atctwo/watch-II/main/states/state_weather.cpp

#include "states.h"

void getLatLong(double &latitude, double &longitude)
{
    EXT_RAM_ATTR latitude = 0;
    EXT_RAM_ATTR longitude = 0;

    if (watch2::wifi_state != 3) // wifi not connected
    {
        ESP_LOGD(WATCH2_TAG, "[weather] not connected to wifi");
    }
    else // wifi is connected
    {
        ESP_LOGD(WATCH2_TAG, "[weather] getting current weather");

        HTTPClient *http = new HTTPClient();
        char server[150];
        std::string api_key = watch2::getApiKey("openweather");
        ESP_LOGD(WATCH2_TAG, "[weather] key: %s", api_key.c_str());
        sprintf(server, "http://api.openweathermap.org/data/2.5/weather?q=%s&appid=%s", watch2::weather_location.c_str(), api_key.c_str());
        ESP_LOGD(WATCH2_TAG, "[weather] server request: %s", server);

        // connect to server
        ESP_LOGD(WATCH2_TAG, "[weather] connecting to server");
        http->begin(watch2::wifi_client, server);
        int http_code = http->GET();
        if (http_code)
        {
            ESP_LOGD(WATCH2_TAG, "[weather] connected to server");
            ESP_LOGD(WATCH2_TAG, "[weather] http code: %d (%s)", http_code, http->errorToString(http_code));

            if (http_code > 0)
            {
                if (http_code == HTTP_CODE_OK)
                {
                    // get server response
                    String res = http->getString();
                    ESP_LOGD(WATCH2_TAG, "[weather] response:");
                    ESP_LOGD(WATCH2_TAG, "%s", res.c_str());

                    // parse returned json
                    cJSON *weather_data = cJSON_Parse(res.c_str());
                    if (weather_data)
                    {
                        // get coord object
                        cJSON *coord_object = cJSON_GetObjectItem(weather_data, "coord");
                        if (coord_object)
                        {
                            // get the latitude and longitude
                            latitude = cJSON_GetObjectItem(coord_object, "lat")->valuedouble;
                            longitude = cJSON_GetObjectItem(coord_object, "lon")->valuedouble;
                        }
                        else
                        {
                            ESP_LOGD(WATCH2_TAG, "[weather] failed to get coord object");
                        }                        
                    }
                    else
                    {
                        ESP_LOGD(WATCH2_TAG, "[weather] failed to parse response");
                    }
                    
                    // free memory used by parsed json
                    cJSON_Delete(weather_data);
                }
            }
            else ESP_LOGD(WATCH2_TAG, "[weather] ???");
            
        }
        else
        {
            ESP_LOGD(WATCH2_TAG, "[weather] failed to connect");
        }

        delete http;
        ESP_LOGD(WATCH2_TAG, "[weather] finished");
    }
    
}

cJSON *getForecast(double latitude, double longitude)
{
    cJSON *forecast = NULL;

    if (watch2::wifi_state != 3) // wifi not connected
    {
        ESP_LOGD(WATCH2_TAG, "[weather] not connected to wifi");
    }
    else // wifi is connected
    {
        ESP_LOGD(WATCH2_TAG, "[weather] getting current weather");

        HTTPClient *http = new HTTPClient();
        char server[175];
        std::string api_key = watch2::getApiKey("openweather");
        ESP_LOGD(WATCH2_TAG, "[weather] key: %s", api_key.c_str());
        sprintf(server, "http://api.openweathermap.org/data/2.5/onecall?lat=%f&lon=%f&exclude=minutely,current,hourly&appid=%s", latitude, longitude, api_key.c_str());
        ESP_LOGD(WATCH2_TAG, "[weather] server request: %s", server);

        // connect to server
        ESP_LOGD(WATCH2_TAG, "[weather] connecting to server");
        http->begin(watch2::wifi_client, server);
        int http_code = http->GET();
        if (http_code)
        {
            ESP_LOGD(WATCH2_TAG, "[weather] connected to server");
            ESP_LOGD(WATCH2_TAG, "[weather] http code: %d (%s)", http_code, http->errorToString(http_code));

            if (http_code > 0)
            {
                if (http_code == HTTP_CODE_OK)
                {
                    // get server response
                    String res = http->getString();
                    ESP_LOGD(WATCH2_TAG, "[weather] response:");
                    ESP_LOGD(WATCH2_TAG, "%s", res.c_str());

                    // parse returned json
                    forecast = cJSON_Parse(res.c_str());
                    if (forecast)
                    {
                        ESP_LOGD(WATCH2_TAG, "[weather] parsed response successfully");                      
                    }
                    else
                    {
                        ESP_LOGD(WATCH2_TAG, "[weather] failed to parse response");
                    }
                }
            }
            else ESP_LOGD(WATCH2_TAG, "[weather] ???");
            
        }
        else
        {
            ESP_LOGD(WATCH2_TAG, "[weather] failed to connect");
        }

        delete http;
        ESP_LOGD(WATCH2_TAG, "hi");
    }

    ESP_LOGD(WATCH2_TAG, "[weather] finished");
    ESP_LOGD(WATCH2_TAG, "aaa");
    return forecast;
    
}

cJSON *getDailyArray(cJSON *forecast)
{
    cJSON *daily_array;

    if (forecast)
    {
        daily_array = cJSON_GetObjectItem(forecast, "daily");
        if (!daily_array) ESP_LOGD(WATCH2_TAG, "[weather] couldn't get daily array");
    }
    else
    {
        ESP_LOGD(WATCH2_TAG, "[weather] forecast is null");
    }

    return daily_array;
}

void state_func_weather()
{

    static cJSON *forecast;
    static cJSON *daily_array;
    static uint8_t selected_day = 0;
    static uint8_t day_page = 0;
    static double latitude = 0;
    static double longitude = 0;
    static uint8_t selected_x = 0;
    static uint8_t selected_y = 0;

    static uint8_t padding = 10;
    static uint8_t button_icon_size = 20;
    static uint16_t day_width = (SCREEN_WIDTH / 2) - (padding * 1.5);
    static uint16_t day_height = (SCREEN_HEIGHT - watch2::top_thing_height - button_icon_size - (padding * 5)) / 4;
    static uint16_t day_radius = 7;
    static TFT_eSprite wind_arrow = TFT_eSprite(&watch2::oled);

    if (watch2::states[watch2::state].variant == 0) // 8 day forecast
    {
        if (!watch2::state_init)
        {
            if (watch2::wifi_state != 3) // not connected to wifi
            {
                watch2::dimScreen(true, 250);
                if (watch2::messageBox("Not connected to\nWifi :(") == 0) 
                {
                    watch2::switchState(-1);
                    return;
                }
            }

            if (watch2::weather_location.isEmpty()) // if no weather location has been set
            {
                ESP_LOGD(WATCH2_TAG, "[weather] location has not been set");

                watch2::dimScreen(true, 250);
                if (watch2::messageBox("Location isn't set.\nDo you want to\nset it?", {"Yes", "No"}) == 0) 
                {
                    std::string location = watch2::textFieldDialogue("Location", watch2::weather_location.c_str());
                    if (location.empty())
                    {
                        // do nothing
                    }
                    else
                    {
                        watch2::weather_location = String(location.c_str());
                        watch2::preferences.begin("watch2");
                        watch2::preferences.putString("weather_city", watch2::weather_location); 
                        watch2::preferences.end();
                    }
                }
            }
            else
            {
                // get latitude and longitude
                getLatLong(latitude, longitude);
                ESP_LOGD(WATCH2_TAG, "[weather] latitude: %f, longitude: %f", latitude, longitude);

                // get forecast
                forecast = getForecast(latitude, longitude);
                daily_array = getDailyArray(forecast);
            }

            // set up wind arrow
            wind_arrow.setColorDepth(16);
            wind_arrow.createSprite(20, 20);
            wind_arrow.setPivot(10, 10);
            wind_arrow.fillSprite(BLACK);
            watch2::drawImage((*watch2::icons)["wind_arrow"], 0, 0, 1.0, 0, wind_arrow);
        }

        if (dpad_left_active())
        {
            if (selected_x == 0) selected_x = 1;
            else selected_x--;
        }
        if (dpad_right_active())
        {
            if (selected_x == 1) selected_x = 0;
            else selected_x++;
        }
        if (dpad_up_active())
        {
            if (selected_y == 0) selected_y = 4;
            else selected_y--;
        }
        if (dpad_down_active())
        {
            if (selected_y == 4) selected_y = 0;
            else selected_y++;
        }

        if (dpad_enter_active())
        {
            if (selected_x == 0 && selected_y == 0) // update location
            {
                std::string location = watch2::textFieldDialogue("Location", watch2::weather_location.c_str());
                if (location.empty())
                {
                    // do nothing
                }
                else
                {
                    watch2::weather_location = String(location.c_str());
                    watch2::preferences.begin("watch2");
                    watch2::preferences.putString("weather_city", watch2::weather_location); 
                    watch2::preferences.end();
                }
            }

            else if (selected_x == 1 && selected_y == 0) // exit app
            {
                if (forecast) cJSON_Delete(forecast);
                watch2::switchState(-1);
            }

            else {

                selected_day = ((selected_y - 1) * 2) + selected_x;
                watch2::switchState(watch2::state, 1);  // switch to details

            }
        }

        draw(dpad_any_active(), {

            // draw location
            watch2::oled.setTextColor(WHITE, BLACK);
            watch2::oled.setCursor(0, watch2::top_thing_height);
            watch2::oled.print(watch2::weather_location);

            // draw icons
            watch2::oled.drawBitmap(
                SCREEN_WIDTH - button_icon_size, watch2::top_thing_height, 
                (*watch2::small_icons)["key_cancel"].data(), button_icon_size, button_icon_size, (selected_y == 0 && selected_x == 1)?watch2::themecolour:WHITE
            );
            watch2::oled.drawBitmap(
                SCREEN_WIDTH - (button_icon_size * 2) - padding, watch2::top_thing_height, 
                (*watch2::small_icons)["key_symbols"].data(), button_icon_size, button_icon_size, (selected_y == 0 && selected_x == 0)?watch2::themecolour:WHITE
            );

            // draw days
            uint16_t x = padding, y = watch2::top_thing_height + button_icon_size + padding;
            for (uint8_t i = 0; i < 8; i++)
            {
                // numbers
                uint8_t current_x = i % 2;
                uint8_t current_y = i / 2;
                uint16_t colour = ( ( current_x == selected_x && current_y == (selected_y - 1)) ? watch2::themecolour : WHITE );

                uint16_t x_position = x + ( (day_width + padding)  * current_x);
                uint16_t y_position = y + ( (day_height + padding) * current_y);

                // draw outline
                watch2::oled.drawRoundRect(x_position, y_position, day_width, day_height, day_radius, colour);

                // draw name and weather
                if (daily_array)
                {
                    cJSON *day_object = cJSON_GetArrayItem(daily_array, i);
                    if (day_object)
                    {
                        // draw day
                        time_t dt = cJSON_GetObjectItem(day_object, "dt")->valueint;
                        watch2::oled.setTextDatum(CL_DATUM);
                        watch2::oled.setTextColor(WHITE, BLACK);
                        watch2::oled.drawString(dayShortStr(weekday(dt)), x_position + padding, y_position + (day_height / 2));
                        watch2::oled.setTextDatum(TL_DATUM);

                        // draw weather icon
                        cJSON *weather_array = cJSON_GetObjectItem(day_object, "weather");
                        if (weather_array)
                        {
                            cJSON *primary_weather = cJSON_GetArrayItem(weather_array, 0);
                            int weather_id = cJSON_GetObjectItem(primary_weather, "id")->valueint;

                            // this assumes all the weather icons are the same dimensions
                            // if the icons were to be different sizes, the next two lines would have to be called
                            // in each switch statement case
                            uint16_t weather_icon_x = (x_position + day_width) - padding - (*watch2::icons)["rain"].width;
                            uint16_t weather_icon_y = (y_position + (day_height / 2)) - ((*watch2::icons)["rain"].height / 2);

                            switch(weather_id / 100)
                            {
                                case 2: // thunder
                                    drawImage((*watch2::icons)["thunder"], weather_icon_x, weather_icon_y);
                                    break;
                                    
                                case 3: // drizzle
                                    drawImage((*watch2::icons)["sun_rain"], weather_icon_x, weather_icon_y);
                                    break;

                                case 5: // rain
                                    drawImage((*watch2::icons)["rain"], weather_icon_x, weather_icon_y);
                                    break;

                                case 6: // snow
                                    drawImage((*watch2::icons)["snow"], weather_icon_x, weather_icon_y);
                                    break;

                                case 7: // atmosphere
                                    drawImage((*watch2::icons)["wind"], weather_icon_x, weather_icon_y);
                                    break;

                                case 8: // clear / clouds
                                    if (weather_id == 800) // clear
                                    {
                                        drawImage((*watch2::icons)["sun"], weather_icon_x, weather_icon_y);
                                    }
                                    else
                                    {
                                        drawImage((*watch2::icons)["sun_cloud"], weather_icon_x, weather_icon_y);
                                    }
                                    break;

                                default:
                                    drawImage((*watch2::icons)["weather_unknown"], weather_icon_x, weather_icon_y);
                                    break;
                            }
                        }
                        else ESP_LOGD(WATCH2_TAG, "[weather] failed to get weather array");
                    }
                    else ESP_LOGD(WATCH2_TAG, "[weather] couldn't get information for day %d", i);

                    
                }
            }

        });
    }
    else if (watch2::states[watch2::state].variant == 1) // daily forecast
    {
        if (!watch2::state_init)
        {
            watch2::oled.setCursor(0, watch2::top_thing_height);
            if (daily_array)
            {
                cJSON *day_object = cJSON_GetArrayItem(daily_array, selected_day);
                if (day_object)
                {
                    // draw date
                    uint32_t dt = cJSON_GetObjectItem(day_object, "dt")->valueint;
                    watch2::oled.setTextColor(watch2::themecolour, BLACK);
                    watch2::oled.printf("%s %d ", dayStr(weekday(dt)), day(dt));
                    watch2::oled.printf("%s\n", monthStr(month(dt)));

                    // draw weather icon
                    cJSON *weather_array = cJSON_GetObjectItem(day_object, "weather");
                    if (weather_array)
                    {
                        cJSON *primary_weather = cJSON_GetArrayItem(weather_array, 0);
                        int weather_id = cJSON_GetObjectItem(primary_weather, "id")->valueint;

                        // this assumes all the weather icons are the same dimensions
                        // if the icons were to be different sizes, the next two lines would have to be called
                        // in each switch statement case
                        uint16_t weather_icon_x = SCREEN_WIDTH - (*watch2::icons)["rain"].width;
                        uint16_t weather_icon_y = watch2::top_thing_height;

                        switch(weather_id / 100)
                        {
                            case 2: // thunder
                                drawImage((*watch2::icons)["thunder"], weather_icon_x, weather_icon_y);
                                break;
                                
                            case 3: // drizzle
                                drawImage((*watch2::icons)["sun_rain"], weather_icon_x, weather_icon_y);
                                break;

                            case 5: // rain
                                drawImage((*watch2::icons)["rain"], weather_icon_x, weather_icon_y);
                                break;

                            case 6: // snow
                                drawImage((*watch2::icons)["snow"], weather_icon_x, weather_icon_y);
                                break;

                            case 7: // atmosphere
                                drawImage((*watch2::icons)["wind"], weather_icon_x, weather_icon_y);
                                break;

                            case 8: // clear / clouds
                                if (weather_id == 800) // clear
                                {
                                    drawImage((*watch2::icons)["sun"], weather_icon_x, weather_icon_y);
                                }
                                else
                                {
                                    drawImage((*watch2::icons)["sun_cloud"], weather_icon_x, weather_icon_y);
                                }
                                break;

                            default:
                                drawImage((*watch2::icons)["weather_unknown"], weather_icon_x, weather_icon_y);
                                break;
                        }
                    }
                    else ESP_LOGD(WATCH2_TAG, "[weather] failed to get weather array");

                    if (day_page == 0)
                    {
                        // draw temperature
                        cJSON *temp = cJSON_GetObjectItem(day_object, "temp");
                        double temp_min = cJSON_GetObjectItem(temp, "min")->valuedouble - 273.5;
                        double temp_max = cJSON_GetObjectItem(temp, "max")->valuedouble - 273.5;
                        double temp_day = cJSON_GetObjectItem(temp, "day")->valuedouble - 273.5;

                        watch2::oled.setTextColor(WHITE, BLACK);
                        watch2::oled.print("High Temp: ");
                        watch2::oled.setTextColor(watch2::themecolour, BLACK);
                        watch2::oled.printf("%0.2f °C\n", temp_max);

                        watch2::oled.setTextColor(WHITE, BLACK);
                        watch2::oled.print("Low Temp: ");
                        watch2::oled.setTextColor(watch2::themecolour, BLACK);
                        watch2::oled.printf("%0.2f °C\n", temp_min);

                        watch2::oled.setTextColor(WHITE, BLACK);
                        watch2::oled.print("Day Temp: ");
                        watch2::oled.setTextColor(watch2::themecolour, BLACK);
                        watch2::oled.printf("%0.2f °C\n", temp_day);

                        // draw pressure
                        uint32_t pressure = cJSON_GetObjectItem(day_object, "pressure")->valueint;
                        watch2::oled.setTextColor(WHITE, BLACK);
                        watch2::oled.print("Pressure: ");
                        watch2::oled.setTextColor(watch2::themecolour, BLACK);
                        watch2::oled.printf("%d hPa\n", pressure);

                        // draw humidity
                        uint32_t humidity = cJSON_GetObjectItem(day_object, "humidity")->valueint;
                        watch2::oled.setTextColor(WHITE, BLACK);
                        watch2::oled.print("Humidity: ");
                        watch2::oled.setTextColor(watch2::themecolour, BLACK);
                        watch2::oled.printf("%d%%\n", humidity);

                        // draw rain
                        cJSON *rain = cJSON_GetObjectItem(day_object, "rain");
                        if (rain)
                        {
                            watch2::oled.setTextColor(WHITE, BLACK);
                            watch2::oled.print("Rain: ");
                            watch2::oled.setTextColor(watch2::themecolour, BLACK);
                            watch2::oled.printf("%0.3f mm\n", rain->valuedouble);
                        }

                        // draw snow
                        cJSON *snow = cJSON_GetObjectItem(day_object, "snow");
                        if (snow)
                        {
                            watch2::oled.setTextColor(WHITE, BLACK);
                            watch2::oled.print("Snow: ");
                            watch2::oled.setTextColor(watch2::themecolour, BLACK);
                            watch2::oled.printf("%0.3f mm\n", snow->valuedouble);
                        }
                    }
                    else if (day_page == 1)
                    {
                        // draw sunrise and sunset
                        uint32_t sunrise = cJSON_GetObjectItem(day_object, "sunrise")->valueint;
                        watch2::oled.setTextColor(WHITE, BLACK);
                        watch2::oled.print("Sunrise: ");
                        watch2::oled.setTextColor(watch2::themecolour, BLACK);
                        watch2::oled.printf("%2d:%2d\n", hour(sunrise), minute(sunrise));

                        uint32_t sunset = cJSON_GetObjectItem(day_object, "sunset")->valueint;
                        watch2::oled.setTextColor(WHITE, BLACK);
                        watch2::oled.print("Sunset:  ");
                        watch2::oled.setTextColor(watch2::themecolour, BLACK);
                        watch2::oled.printf("%2d:%2d\n", hour(sunset), minute(sunset));

                        // draw clouds
                        uint32_t clouds = cJSON_GetObjectItem(day_object, "clouds")->valueint;
                        watch2::oled.setTextColor(WHITE, BLACK);
                        watch2::oled.print("Clouds: ");
                        watch2::oled.setTextColor(watch2::themecolour, BLACK);
                        watch2::oled.printf("%d%%\n", clouds);

                        // draw dew point
                        double dew_point = cJSON_GetObjectItem(day_object, "dew_point")->valuedouble - 273.5;
                        watch2::oled.setTextColor(WHITE, BLACK);
                        watch2::oled.print("Dew Point: ");
                        watch2::oled.setTextColor(watch2::themecolour, BLACK);
                        watch2::oled.printf("%0.2f °C\n", dew_point);

                        // draw wind speed
                        double wind_speed = cJSON_GetObjectItem(day_object, "wind_speed")->valuedouble * MPS_TO_MPH;
                        watch2::oled.setTextColor(WHITE, BLACK);
                        watch2::oled.print("Wind Speed: ");
                        watch2::oled.setTextColor(watch2::themecolour, BLACK);
                        watch2::oled.printf("%0.2f mph\n", wind_speed);

                        // draw wind direction
                        uint32_t wind_deg = cJSON_GetObjectItem(day_object, "wind_deg")->valueint;
                        watch2::oled.setTextColor(WHITE, BLACK);
                        watch2::oled.print("Wind Direction: ");
                        watch2::oled.setTextColor(watch2::themecolour, BLACK);
                        watch2::oled.printf("%d °\n", wind_deg);

                        watch2::oled.setPivot(
                            watch2::oled.textWidth("Wind Direction: 999°") + 20, 
                            watch2::top_thing_height + (watch2::oled.fontHeight() * 6) + 10
                        );
                        wind_arrow.pushRotated(wind_deg, BLACK);
                        //wind_arrow.pushSprite(100, 100);

                        // draw uv index
                        double uvi = cJSON_GetObjectItem(day_object, "uvi")->valuedouble;
                        watch2::oled.setTextColor(WHITE, BLACK);
                        watch2::oled.print("UV Index: ");
                        watch2::oled.setTextColor(watch2::themecolour, BLACK);
                        watch2::oled.printf("%0.2f\n", uvi);
                    }
                }
                else 
                {
                    ESP_LOGD(WATCH2_TAG, "[weather] couldn't get day from array (selected_day: %d)", selected_day);
                    watch2::oled.printf("error: couldn't get \nday from array \n(selected_day: %d)\n", selected_day);
                }
            }
            else 
            {
                ESP_LOGD(WATCH2_TAG, "[weather] invalid daily array");
                watch2::oled.println("error: invalid daily \narray");
            }

            
        }

        if (dpad_left_active() || dpad_right_active())
        {
            if (day_page == 0) day_page = 1;
            else day_page = 0;
            watch2::switchState(watch2::state, 1);
        }

        if (dpad_any_active())
        {
            watch2::switchState(watch2::state, 0);
        }
    }

    watch2::drawTopThing();

}
