atctwo/watch-II/main/states/state_timer.cpp

#include "states.h"

void state_func_timer()
{
    static int selected_timer = -1;
    static int selected_button = 3;
    static int last_selected_timer = -2;
    //0 - hours
    //1 - minutes
    //2 - seconds
    //3 - play / pause (or back if on timer -1)
    //4 - delete (or add if on timer -1)
    EXT_RAM_ATTR static char text_aaaa[150];
    EXT_RAM_ATTR static int16_t x1, y1;
    EXT_RAM_ATTR static uint16_t w=0, h=0;
    EXT_RAM_ATTR static uint16_t width_two_digits = 0, width_two_digits_colon = 0, width_three_digits_colon = 0;

    if (!watch2::state_init)
    {
        //watch2::oled.setFreeFont(&SourceSansPro_Regular6pt7b);

        //calculate sizes of digit things
        watch2::getTextBounds("99", 0, 0, &x1, &y1, &width_two_digits, &h);
        watch2::getTextBounds(": 99", 0, 0, &x1, &y1, &width_two_digits_colon, &h);
        watch2::getTextBounds(": 999", 0, 0, &x1, &y1, &width_three_digits_colon, &h);

    }

    if (dpad_left_active())
    {
        selected_button--;
        if (selected_button < 0) selected_button = 4;
        if (selected_timer == -1 && selected_button < 2) selected_button = 4;
    }

    if (dpad_right_active())
    {
        selected_button++;
        if (selected_button > 4) selected_button = 0;
        if (selected_timer == -1 && selected_button < 2) selected_button = 2;
    }

    if (dpad_down_active())
    {
        if (selected_timer == -1 || selected_button == 3 || selected_button == 4)
        {
            selected_timer++;
            if (selected_timer >= watch2::timers.size()) selected_timer = -1;
        }
        else //decrease time
        {
            if (floor(watch2::timers[selected_timer].duration / 3600) > 0)
            if (selected_button == 0) watch2::timers[selected_timer].duration -= 3600;      //hours
            if (floor(watch2::timers[selected_timer].duration % 3600 / 60) > 0)
            if (selected_button == 1) watch2::timers[selected_timer].duration -= 60;        //minutes
            if (floor(watch2::timers[selected_timer].duration % 3600 % 60) > 0)
            if (selected_button == 2) watch2::timers[selected_timer].duration -= 1;         //seconds
            if (watch2::timers[selected_timer].alarm_id != 255) Alarm.write(watch2::timers[selected_timer].alarm_id, watch2::timers[selected_timer].duration); //reset timer with new duration
            else watch2::timers[selected_timer].initial_duration = watch2::timers[selected_timer].duration;
        }
    }

    if (dpad_up_active())
    {
        if (selected_timer == -1 || selected_button == 3 || selected_button == 4)
        {
            selected_timer--;
            if (selected_timer < -1) selected_timer = watch2::timers.size() - 1;
        }
        else //increase time
        {
            if (selected_button == 0) watch2::timers[selected_timer].duration += 3600;      //hours
            if (selected_button == 1) watch2::timers[selected_timer].duration += 60;        //minutes
            if (selected_button == 2) watch2::timers[selected_timer].duration += 1;         //seconds
            if (watch2::timers[selected_timer].alarm_id != 255) Alarm.write(watch2::timers[selected_timer].alarm_id, watch2::timers[selected_timer].duration); //reset timer with new duration
            else watch2::timers[selected_timer].initial_duration = watch2::timers[selected_timer].duration;
        }
    }

    if (dpad_enter_active())
    {
        if (selected_timer == -1)
        {
            //add new timer
            if (selected_button == 4)
            {
                watch2::timers.push_back({
                    30,     //duration in seconds
                    30,     //initial duration (used when a timer ends)
                    255,    //alarm id (255 means that no TimeAlarms timer has been created)
                    -1,     //time started
                    [](){   //function to execute once timer has ended
                        AlarmID_t id = Alarm.getTriggeredAlarmId();
                        int timer_id = -1;
                        for (int i = 0; i < watch2::timers.size(); i++)
                        {
                            if (watch2::timers[i].alarm_id == id)
                            {
                                timer_id = i;
                            }
                        }
                        watch2::timers[timer_id].alarm_id = 255;
                        watch2::timers[timer_id].time_started = -1;
                        watch2::timers[timer_id].duration = watch2::timers[timer_id].initial_duration;
                        watch2::timer_trigger_status = 1;
                        watch2::timer_trigger_id = timer_id;
                    },
                    -1      //last value (used for redrawing remaining time)
                });
            }
            else if (selected_button == 2)
            {
                // change timer music
                ESP_LOGD(WATCH2_TAG, "[timers] changing music");
                std::string new_music = watch2::beginFileSelect();
                ESP_LOGD(WATCH2_TAG, "[timers] new music to %s", new_music.c_str());
                watch2::timer_music = String(new_music.c_str());
                ESP_LOGD(WATCH2_TAG, "[timers] changed music to %s", watch2::timer_music.c_str());

                watch2::preferences.begin("watch2");
                watch2::preferences.putString("timer_music", watch2::timer_music);
                watch2::preferences.end();
                ESP_LOGD(WATCH2_TAG, "[timers] updated preferences store");
            }
        }
        else
        {
            if (selected_button == 3) // play / pause timer
            {
                if (watch2::timers[selected_timer].alarm_id == 255) //start timer
                {
                    //create a TimeAlarms timer
                    AlarmID_t id = Alarm.timerOnce(
                        watch2::timers[selected_timer].duration,             //duration in seconds
                        watch2::timers[selected_timer].on_tick_handler       //function to call after time has elapsed
                    );

                    //store timer metadata
                    watch2::timers[selected_timer].alarm_id = id;
                    watch2::timers[selected_timer].time_started = now();
                }
                else                                      //pause timer
                {
                    //store time remaining
                    time_t time_remaining = ( watch2::timers[selected_timer].time_started + Alarm.read(watch2::timers[selected_timer].alarm_id ) ) - now();
                    watch2::timers[selected_timer].duration = time_remaining;

                    //free alarm id (essentially destroying the TimeAlarm timer) and reset stored alarm id and time started
                    Alarm.free(watch2::timers[selected_timer].alarm_id);
                    watch2::timers[selected_timer].alarm_id = 255;
                    watch2::timers[selected_timer].time_started = -1;
                }
            }
            if (selected_button == 4) // remove timer
            {
                //store selected timer
                AlarmID_t whee = selected_timer;

                //change selecte timer to previous timer
                selected_timer--;

                //free alarm id
                Alarm.free(watch2::timers[whee].alarm_id);

                //remove timer from timers
                watch2::timers.erase(watch2::timers.begin() + whee);

                //clear screen
                watch2::oled.fillScreen(BLACK);
            }
        }
    }

    //draw timers
    if (1)
    {
        int timer_x = 2;
        int timer_y = watch2::top_thing_height;
        int timer_w = SCREEN_WIDTH - (timer_x * 2);
        int timer_h = SCREEN_HEIGHT - timer_y;
        int icon_radius = 8;
        int radius = 4;
        int icon_spacing = 3;
        int icon_size = 20;
        int timer_edge = timer_x + timer_w;
        uint16_t working_button_colour = WHITE;
        uint16_t working_timer_colour = WHITE;

        draw(dpad_any_active(), {

            //set colour of row
            working_timer_colour = (selected_timer == -1) ? watch2::themecolour : WHITE;

            //draw header
            watch2::oled.setTextColor(working_timer_colour, BLACK);
            watch2::oled.setCursor(timer_x, timer_y);
            watch2::oled.print("Timers");

            //set colour of music button
            working_button_colour = (selected_button <= 2 && selected_timer == -1) ? watch2::themecolour : WHITE;

            //draw music button
            watch2::oled.drawBitmap(
                timer_edge - (icon_size * 3) - (icon_spacing * 8),
                timer_y,
                (*watch2::small_icons)["small_audio"].data(),
                icon_size,
                icon_size,
                working_button_colour
            );

            //set colour of back button
            working_button_colour = (selected_button == 3 && selected_timer == -1) ? watch2::themecolour : WHITE;

            //draw back button
            watch2::oled.drawBitmap(
                timer_edge - (icon_size * 2) - (icon_spacing * 5),
                timer_y,
                (*watch2::small_icons)["back"].data(),
                icon_size,
                icon_size,
                working_button_colour
            );

            //set colour of add button
            working_button_colour = (selected_button == 4 && selected_timer == -1) ? watch2::themecolour : WHITE;

            //draw add button
            watch2::oled.drawBitmap(
                timer_edge - icon_size - (icon_spacing * 2),
                timer_y,
                (*watch2::small_icons)["add"].data(),
                icon_size,
                icon_size,
                working_button_colour
            );
        });

        //draw timers
        for (int i = 0; i < watch2::timers.size(); i++)
        {
            timer_y += watch2::oled.fontHeight() + (icon_spacing * 2);

            time_t current_time = (watch2::timers[i].alarm_id == 255) ? watch2::timers[i].duration : ( watch2::timers[i].time_started + Alarm.read(watch2::timers[i].alarm_id ) ) - now();
            //if this is the state's first frame, or the time of the timer has changed,
            //or this is the selected timer and any button has been pressed
            draw(dpad_any_active() || current_time != watch2::timers[i].last_value, {
                //clear previous text
                watch2::oled.fillRect(timer_x, timer_y, timer_w - (icon_spacing * 6) - (icon_size * 2), watch2::oled.fontHeight(), BLACK);

                //set colour of row
                working_timer_colour = (selected_timer == i) ? watch2::themecolour : WHITE;

                //get time to display
                time_t time_left = (watch2::timers[i].alarm_id == 255) ? watch2::timers[i].duration : ( watch2::timers[i].time_started + Alarm.read(watch2::timers[i].alarm_id ) ) - now();
                time_t time_left_hrs = floor(time_left / 3600);
                time_t time_left_min = floor(time_left % 3600 / 60);
                time_t time_left_sec = floor(time_left % 3600 % 60);

                /*
                watch2::getTextBounds("99", 0, 0, &x1, &y1, &width_two_digits, &h);
                watch2::getTextBounds(":99", 0, 0, &x1, &y1, &width_two_digits_colon, &h);
                watch2::getTextBounds(":999", 0, 0, &x1, &y1, &width_three_digits_colon, &h);
                */

                //print hours
                watch2::oled.setCursor(timer_x, timer_y);
                watch2::oled.setTextColor(working_timer_colour, BLACK);
                watch2::oled.printf("%02d", time_left_hrs);
                working_button_colour = (selected_button == 0 && selected_timer == i) ? watch2::themecolour : BLACK;
                watch2::oled.drawRoundRect(timer_x - 1, timer_y - 1, width_two_digits + 4, watch2::oled.fontHeight(), icon_radius, working_button_colour);

                //print minutes
                watch2::oled.setCursor(timer_x + (width_two_digits) + 4, timer_y);
                watch2::oled.printf(": %02d", time_left_min);
                working_button_colour = (selected_button == 1 && selected_timer == i) ? watch2::themecolour : BLACK;
                watch2::oled.drawRoundRect(timer_x + (width_two_digits) + 4 - 1, timer_y - 1, width_two_digits_colon + 5, watch2::oled.fontHeight(), icon_radius, working_button_colour);

                //print seconds
                watch2::oled.setCursor(timer_x + width_two_digits + width_two_digits_colon + 2 + 7, timer_y);
                watch2::oled.printf(": %02d", time_left_sec);
                working_button_colour = (selected_button == 2 && selected_timer == i) ? watch2::themecolour : BLACK;
                watch2::oled.drawRoundRect(timer_x + width_two_digits + width_two_digits_colon + 2 + 7 - 1, timer_y - 1, width_two_digits_colon + 5, watch2::oled.fontHeight(), icon_radius, working_button_colour);

                //set colour of play / pause button
                working_button_colour = (selected_button == 3 && selected_timer == i) ? watch2::themecolour : WHITE;

                //draw play / pause button
                watch2::oled.drawBitmap(
                    timer_edge - (icon_size * 2) - (icon_spacing * 5),
                    timer_y,
                    (watch2::timers[i].alarm_id == 255) ? (*watch2::small_icons)["play"].data() : (*watch2::small_icons)["pause"].data(),
                    icon_size,
                    icon_size,
                    working_button_colour
                );

                //set colour of delete button
                working_button_colour = (selected_button == 4 && selected_timer == i) ? watch2::themecolour : WHITE;

                //draw delete button
                watch2::oled.drawBitmap(
                    timer_edge - icon_size - (icon_spacing * 2),
                    timer_y,
                    (*watch2::small_icons)["key_cancel"].data(),
                    icon_size,
                    icon_size,
                    working_button_colour
                );

                watch2::timers[i].last_value = (watch2::timers[i].alarm_id == 255) ? watch2::timers[i].duration : ( watch2::timers[i].time_started + Alarm.read(watch2::timers[i].alarm_id ) ) - now();

            });

        }

    }

    watch2::drawTopThing();

    if (dpad_enter_active())
    {
        if (selected_timer == -1)
        {
            //go back to state menu
            if (selected_button < 4) watch2::switchState(-1);
        }
    }

    last_selected_timer = selected_timer;
}
