atctwo/watch-II/main/states/states.cpp

#include "../watch2.h"
#include "states.h"

namespace watch2
{

    std::vector<stateMeta> states = {

        stateMeta("Initial State", state_func_init, "init.bmp", 0, false, true),
        stateMeta("Watch Face", state_func_watch_face, "watch"),
        stateMeta("State Menu", state_func_state_menu, "menu", 0, false, true),
        stateMeta("Settings", state_func_settings, "settings"),

        stateMeta("Calculator", state_func_calc, "calculator"),
        stateMeta("Stopwatch", state_func_stopwatch, "stopwatch"),
        stateMeta("Timer", state_func_timer, "timer"),
        stateMeta("Alarms", state_func_alarms, "alarms"),
        stateMeta("File Browser", state_func_SDtest, "file_browser"),
        stateMeta("Notepad", state_func_notepad, "notepad"),
        stateMeta("IR remote", state_func_ir_remote, "ir_remote"),
        stateMeta("Image Viewer", state_func_image_viewer, "image_viewer"),
        stateMeta("Weather", state_func_weather, "weather"),
        stateMeta("Wikipedia", state_func_wiki, "wikipedia"),
        stateMeta("Quiz Thingy", state_func_quiz, "quiz"),
        stateMeta("Reddit", state_func_reddit),
        stateMeta("Music Player", state_func_music_player, "music_player"),
        stateMeta("Radio", state_func_radio, "radio"),
        //stateMeta("Recorder", state_func_recorder),
        stateMeta("Bluetooth Remote", state_func_bt_remote, "ble_remote"),
        stateMeta("Sensor Thing", state_func_sensor, "sensors"),
        stateMeta("Tetris", state_func_tetris, "ltris"),
        stateMeta("Snek 2", state_func_snek, "snake"),
        stateMeta("Blackjack", state_func_blackjack, "cards")
        // //stateMeta("NES", state_func_nes, "nes")

    };

}
