atctwo/watch-II/main/watch2_files.cpp

/**
 * @file watch2_files.cpp
 * @author atctwo
 * @brief functions for file system access
 * @version 0.1
 * @date 2020-11-21
 * 
 * @copyright Copyright (c) 2020 atctwo
 * 
 */

#include "watch2.h"

namespace watch2 {

    // files
    EXT_RAM_ATTR int sd_state = 0;
    EXT_RAM_ATTR bool spiffs_state = 0;
    EXT_RAM_ATTR int file_select_status = 0;
    EXT_RAM_ATTR std::string file_path = "/";
    EXT_RAM_ATTR bool file_select_dir_list_init = false;
    
    //SdFat sdcard(&*vspi);
    //Adafruit_ImageReader reader(SD);

    int initSD(bool handleCS)
    {
        if (sd_state == 1)
        {
            // sd card is already initalised
            ESP_LOGW(WATCH2_TAG, "[initSD] sd is already mounted");
            return 1;
        }

        int no = 0;

        //enable the sd card
        digitalWrite(cs, HIGH);
        digitalWrite(sdcs, LOW);

        //initalise the sd card
        //if(!sdcard.begin(sdcs, SPISettings(9000000, MSBFIRST, SPI_MODE0))){
        if(!SD.begin(sdcs, *watch2::vspi, 4000000U)){

            //card couldn't mount
            ESP_LOGW(WATCH2_TAG, "[initSD] Couldn't mount SD card");
            // ESP_LOGD(WATCH2_TAG, "\tError code: ");
            // ESP_LOGD(WATCH2_TAG, "0x%x", sdcard.cardErrorCode());
            // ESP_LOGD(WATCH2_TAG, "\tError data: ");
            // ESP_LOGD(WATCH2_TAG, "0x%x", sdcard.cardErrorData());
            no = 0;

        }
        else
        {

            //card mounted successfully
            ESP_LOGD(WATCH2_TAG, "[initSD] Successfully mounted SD card");
            ESP_LOGD(WATCH2_TAG, "Card size: %u", SD.cardSize());
            //sdcard.ls(LS_R | LS_DATE | LS_SIZE);
            no = 1;

        }

        //if there is no sd card inserted, set no to 2
        //if (!digitalRead(sdcd)) no = 2;

        //set global sd state variable, and return
        sd_state = no;
        return no;
    }
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
